Alexandre-Arrive/WallEE-Culture-Maker/Circuits électroniques/Circuit_conv_3.3V_5V/image_conv_circuit.PNG

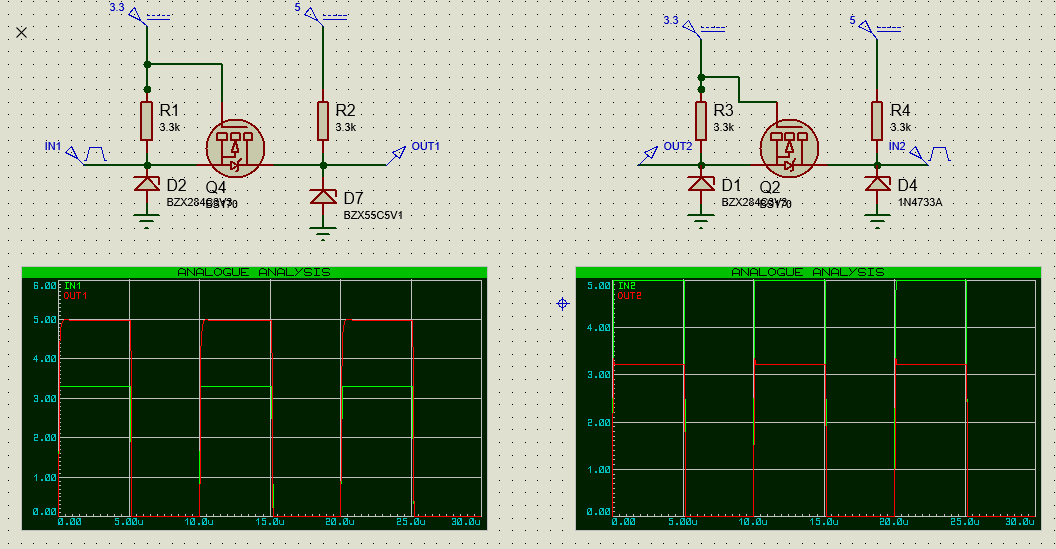
Circuits électroniques/Circuit_conv_3.3V_5V/image_conv_circuit.PNG
