Alexandre-Arrive/WallEE-Culture-Maker/Circuits électroniques/Circuit_led/image_led_circuit.PNG

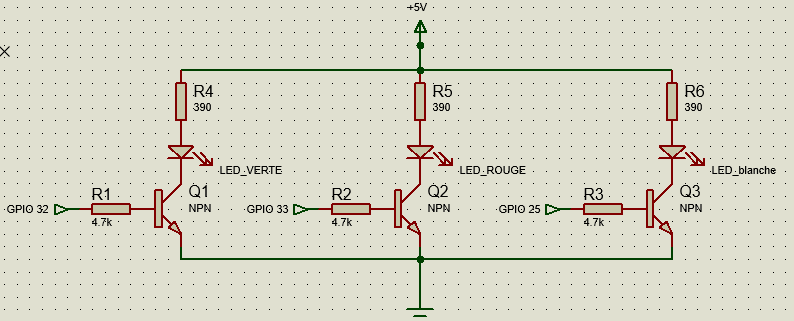
Circuits électroniques/Circuit_led/image_led_circuit.PNG
