Alexandre-Arrive/WallEE-Culture-Maker/Circuits électroniques/PCB_face_avant/image_front_circuit.PNG

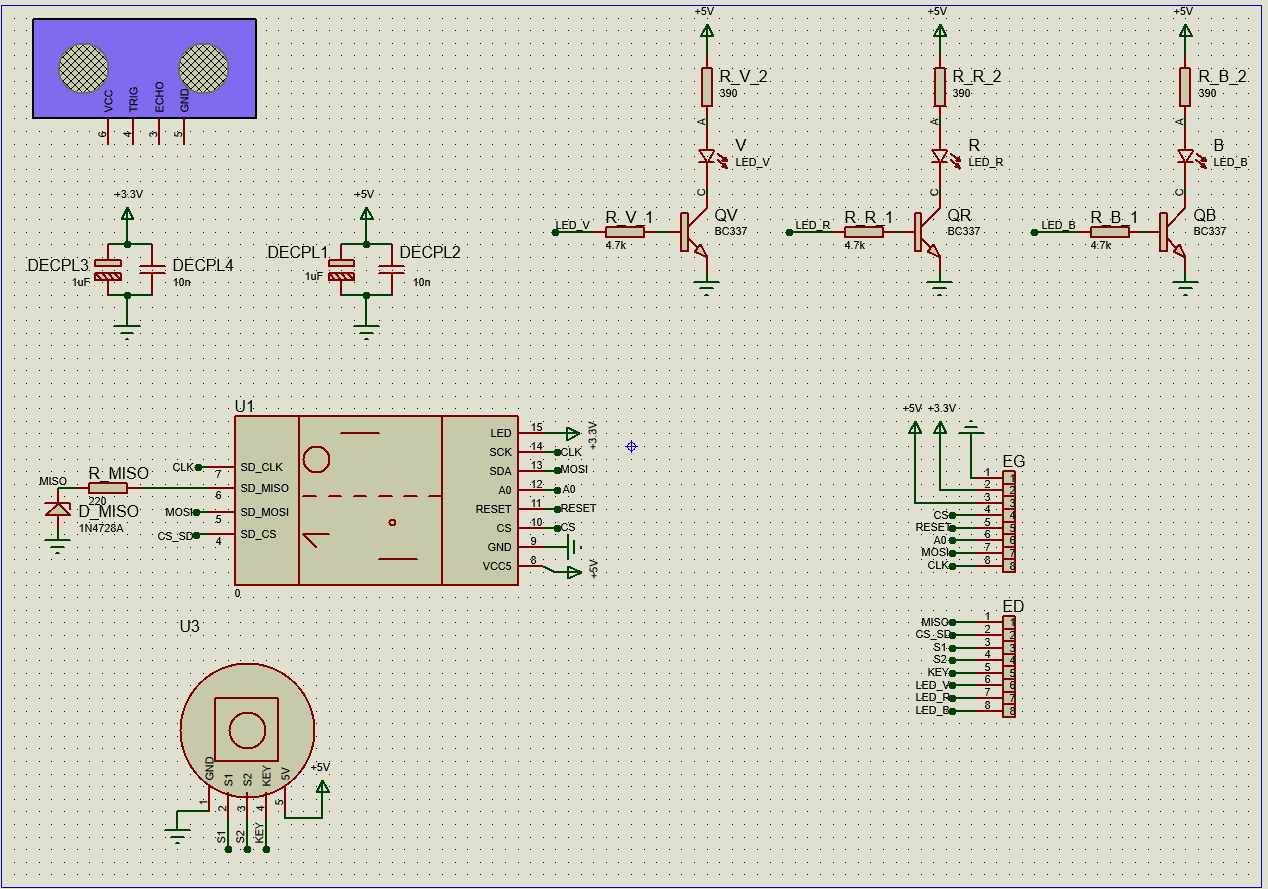
Circuits électroniques/PCB_face_avant/image_front_circuit.PNG
