Alexandre-Arrive/WallEE-Culture-Maker/Circuits électroniques/PCB_face_avant/image_front_pcb.PNG

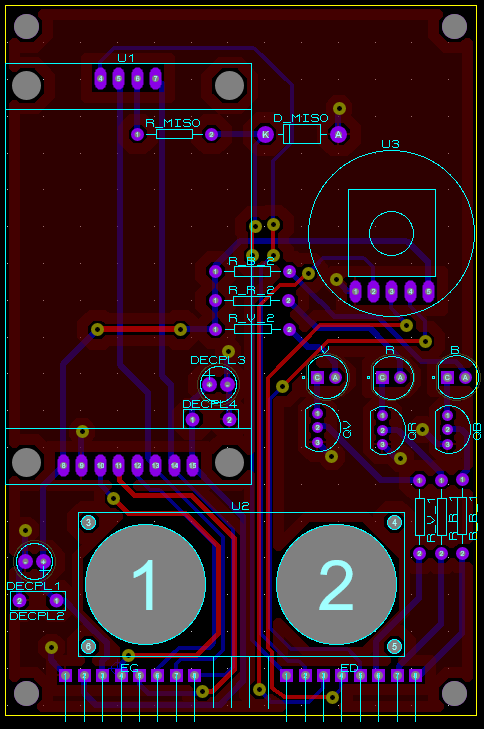
Circuits électroniques/PCB_face_avant/image_front_pcb.PNG
